NacioSystems/DESCODIFICADOR-RDS/Fotos/Baja resolucion/Montaje.jpg

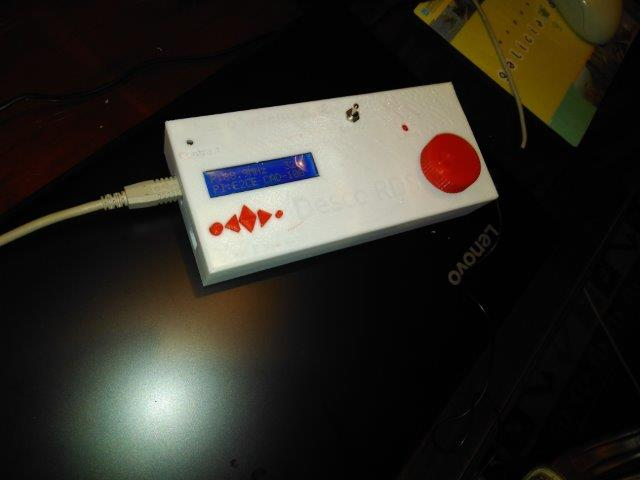
Fotos/Baja resolucion/Montaje.jpg
